FasterEdge/RelayNode-SW2MQTT/firmware/ESP8266/platformio_ide/include/config.h

// ─────────────────────────────────────────────────────────────
// FasterEdge 开源项目
// Github: https://github.com/FasterEdge
// Gitee:  https://gitee.com/FasterEdge
// ─────────────────────────────────────────────────────────────
#pragma once

// Safe defaults: firmware builds, but it will not join Wi-Fi until configured.
#define FE_WIFI_SSID ""
#define FE_WIFI_PASSWORD ""

#define FE_MQTT_HOST "192.168.1.10"
#define FE_MQTT_PORT 1883
#define FE_MQTT_USERNAME ""
#define FE_MQTT_PASSWORD ""

#define FE_MQTT_TOPIC_PREFIX "fasteredge/relaynode/sw2mqtt"
#define FE_MQTT_RETAIN_INPUTS true
#define FE_DEBOUNCE_MS 30U
#define FE_HEARTBEAT_MS 60000UL
